znuh/usb2serial-autovtg/ltspice/uart_ref11.asc

C1: cap; 10n
C2: cap; 100n
C3: cap; 20p
D1: schottky; BAT54
D2: schottky; BAT54
R1: res; 120
R2: res; 10k
R3: res; 2.2Meg
R4: res; 120
R5: res; 270k
R6: res; 120
R7: res; 270k
R8: res; 10k
R9: res; 120
R10: res; 10k
U1: LMV358A
U2: LMV358A
U3: SN74LVC1G17
V1: voltage; PULSE(0 1.8 1m 10n 10n 4.3u 43.4u 10)
V2: voltage; 5
V3: voltage; PULSE(0 1.8 1m 10n 10n 104u 1144u 10)
V4: voltage; PULSE(0 3.3 1.1m 10n 10n 8u 724u 10)
V5: voltage; PULSE(0 3.3 1.1m 10n 10n 1104u 1144u 10)
V6: voltage; 1.8
Named nets: 0, tx, out, load, tx_out, in+, vref
.tran 30m
